darkomenz/firestarter/lasermodule/scanhead_pcb_compact/baseboard/scanhead_pcb.kicad_sch

## KiCad design lasermodule/scanhead_pcb_compact/baseboard/scanhead_pcb.kicad_sch (2023-05-03)

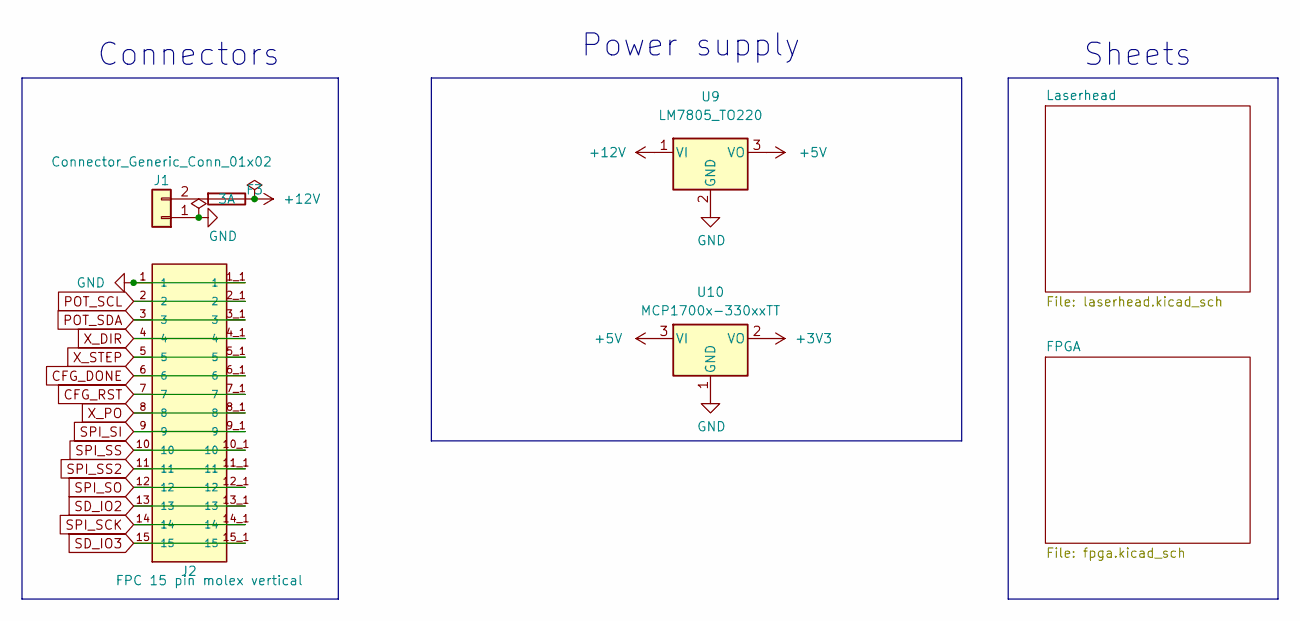
[picture p10: schematic scanhead_pcb.kicad_sch]

Parts:
F3: 3A; Fuse_1206_3216Metric
J1: Connector_Generic_Conn_01x02; AMASS_XT30PW-F_1x02_P2.50mm_Horizontal
J2: FPC 15 pin molex vertical; TE_1-1734248-5; PARTREV E1
U9: LM7805_TO220; TO-220-3_Vertical
U10: MCP1700x-330xxTT; SOT-23

Connections:
+3V3: U10.2 (VO)
+5V: U9.3 (VO), U10.3 (VI)
+12V: F3.1, U9.1 (VI)
CFG_DONE: J2.6, J2.6_1 (6)
CFG_RST: J2.7, J2.7_1 (7)
GND: J1.1, J2.1, J2.1_1 (1), U9.2 (GND), U10.1 (GND)
unnamed: F3.2, J1.2
POT_SCL: J2.2, J2.2_1 (2)
POT_SDA: J2.3, J2.3_1 (3)
SD_IO2: J2.13, J2.13_1 (13)
SD_IO3: J2.15, J2.15_1 (15)
SPI_SCK: J2.14, J2.14_1 (14)
SPI_SI: J2.9, J2.9_1 (9)
SPI_SO: J2.12, J2.12_1 (12)
SPI_SS: J2.10, J2.10_1 (10)
SPI_SS2: J2.11, J2.11_1 (11)
X_DIR: J2.4, J2.4_1 (4)
X_PO: J2.8, J2.8_1 (8)
X_STEP: J2.5, J2.5_1 (5)

Notes on the sheet:
Power supply
Connectors
Sheets
